hixair/Data-center-temperature-monitor/img/IMG_3179.JPG

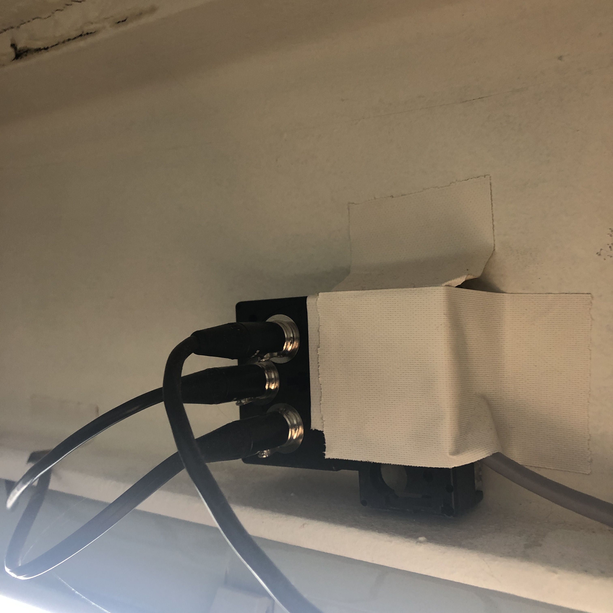
img/IMG_3179.JPG
