hixair/Data-center-temperature-monitor/img/IMG_3180.JPG

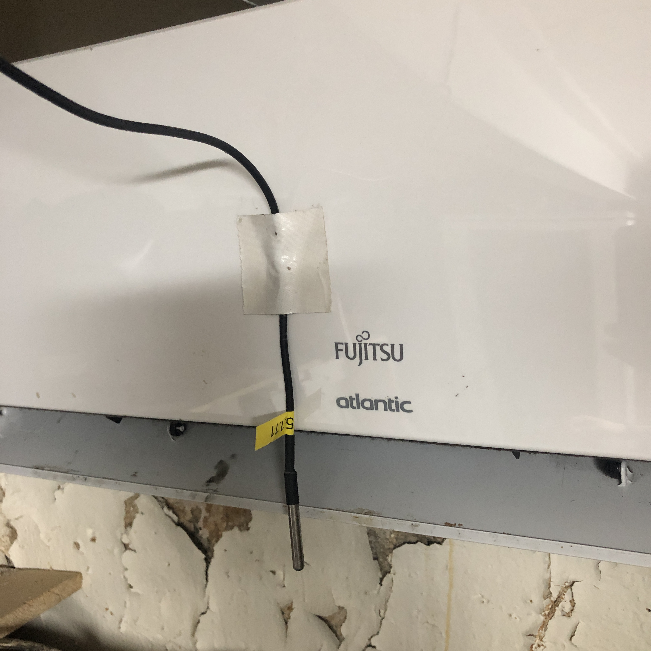
img/IMG_3180.JPG
