hixair/Data-center-temperature-monitor/img/IMG_0295.JPG

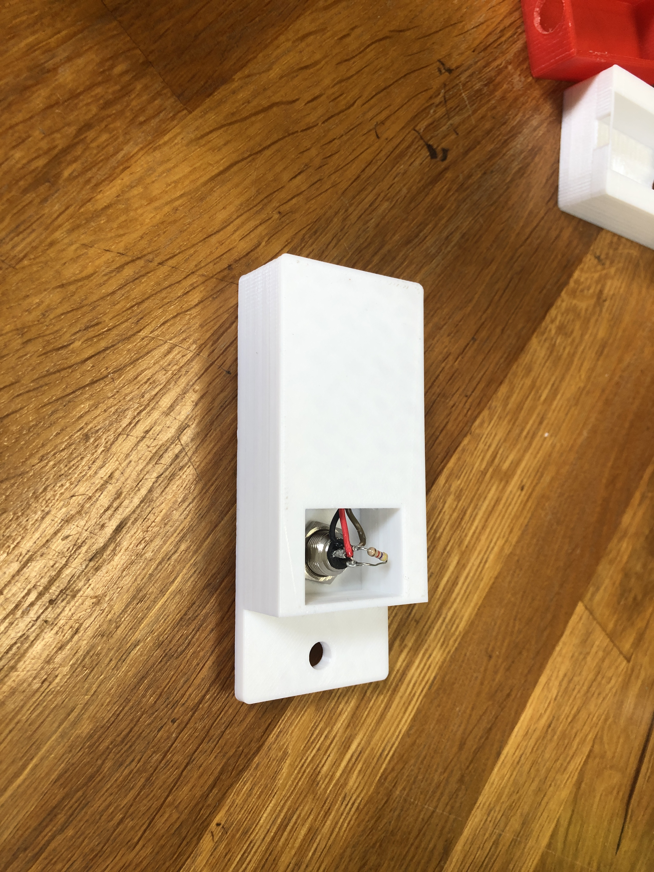
img/IMG_0295.JPG
