hixair/Data-center-temperature-monitor/img/IMG_6995.JPG

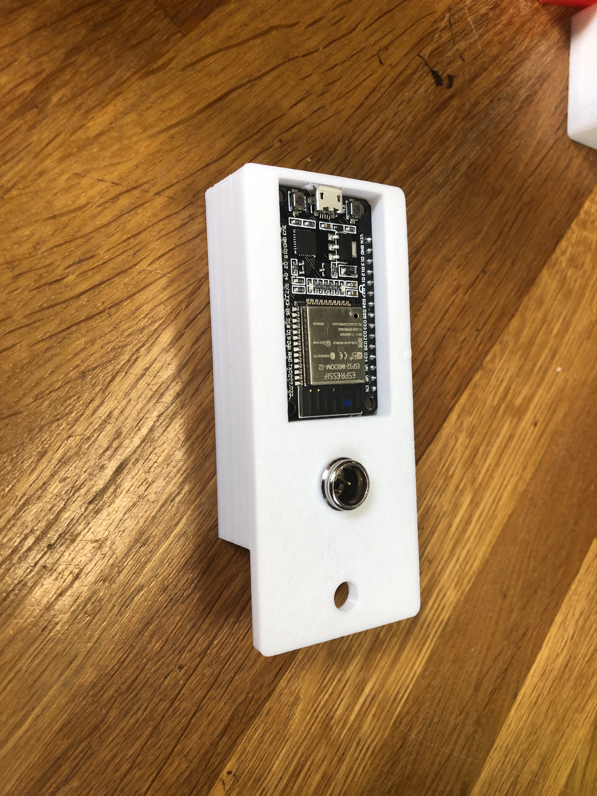
img/IMG_6995.JPG
